takashicompany/endzone34/images/01.jpg

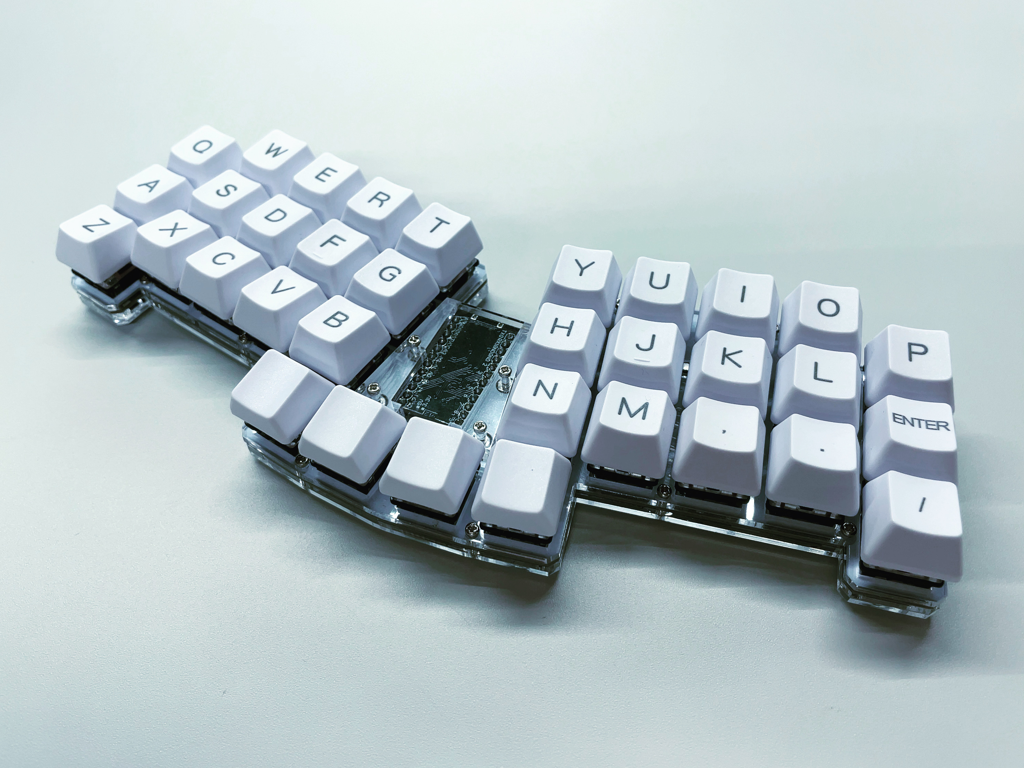
images/01.jpg
