takashicompany/endzone34/images/02.jpg

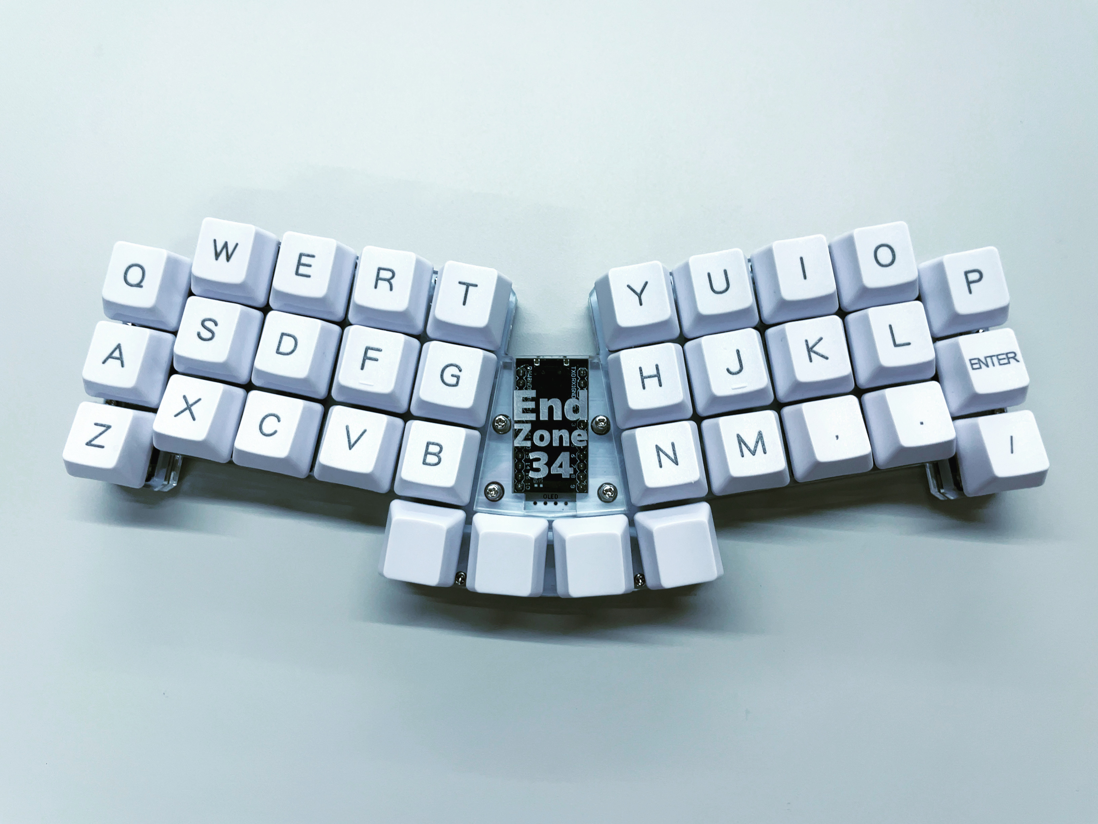
images/02.jpg
