takashicompany/endzone34/images/03.jpg

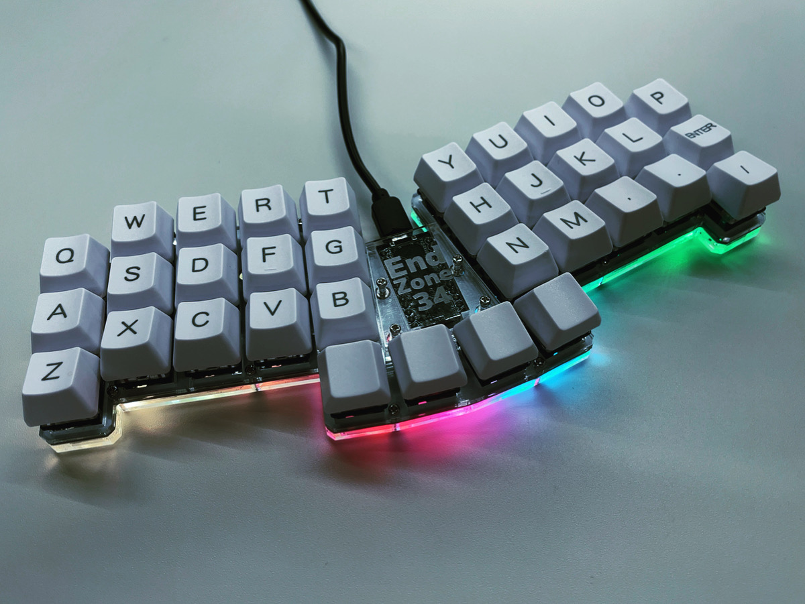
images/03.jpg
