takashicompany/endzone34/images/04.jpg

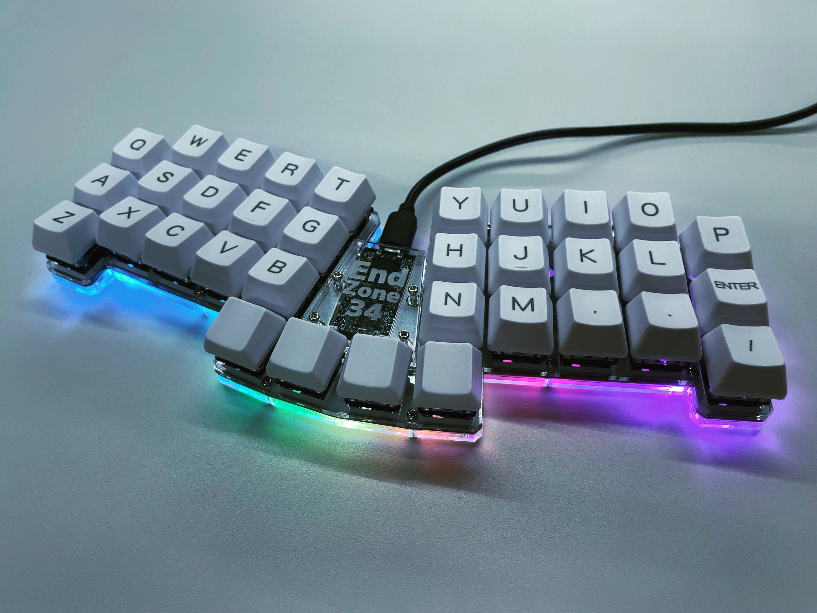
images/04.jpg
