takashicompany/endzone34/images/05.jpg

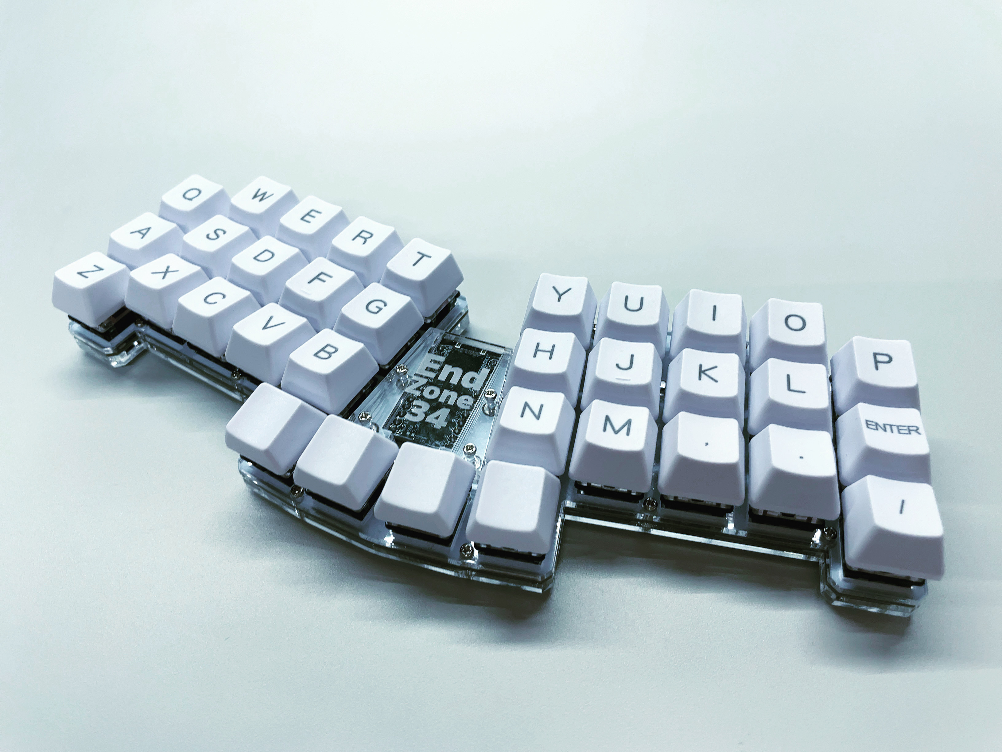
images/05.jpg
