takashicompany/endzone34/images/06.jpg

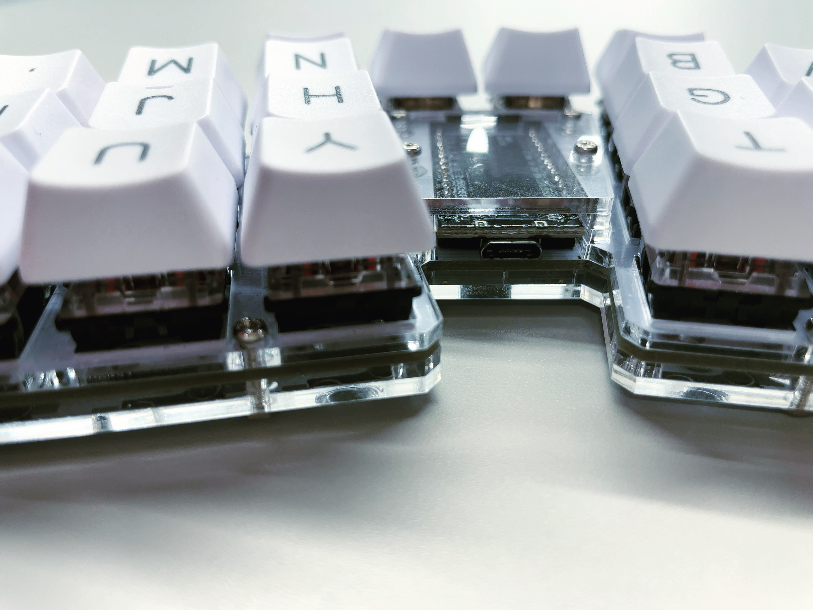
images/06.jpg
