takashicompany/endzone34/images/07.jpg

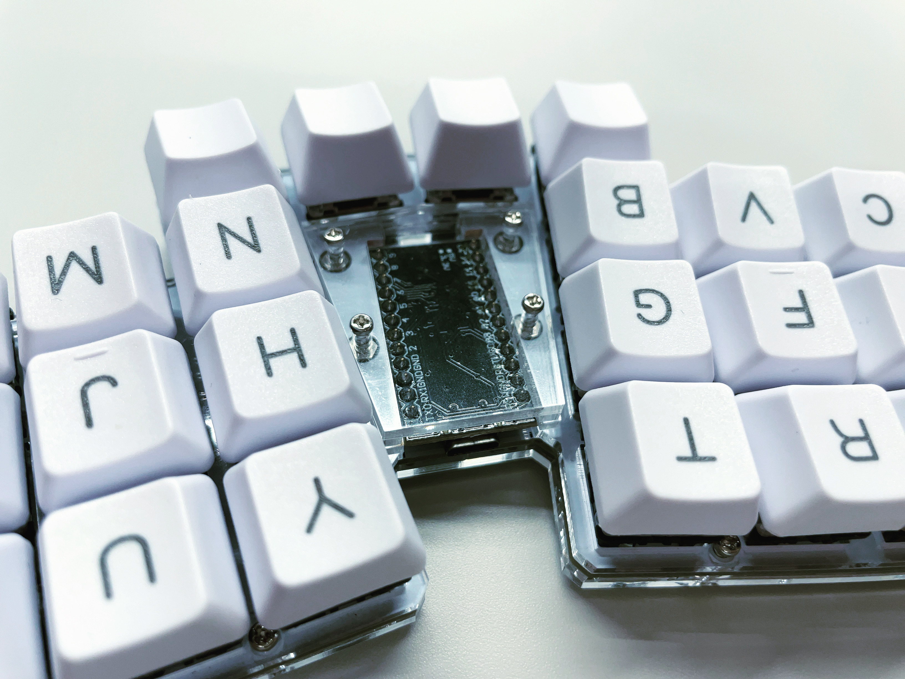
images/07.jpg
