takashicompany/endzone34/images/09.jpg

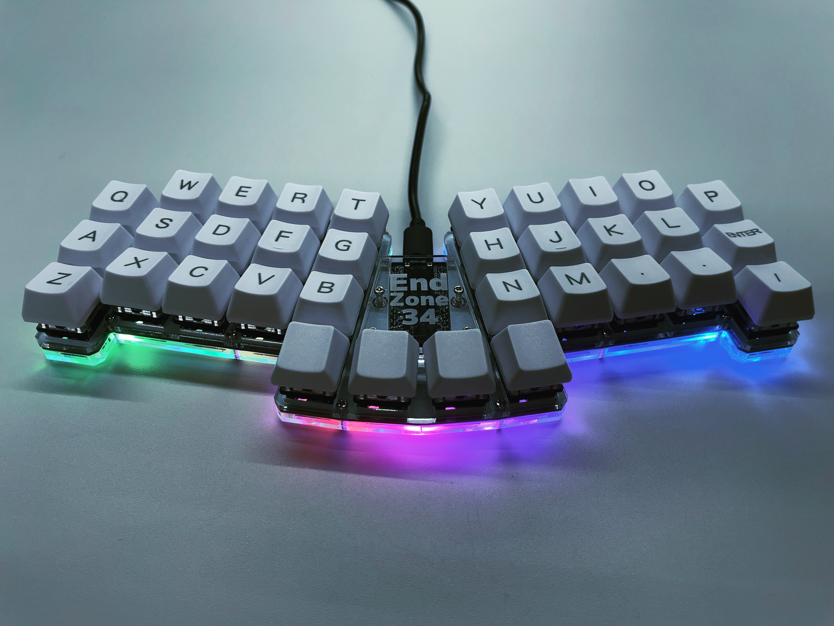
images/09.jpg
