takashicompany/endzone34/images/10.jpg

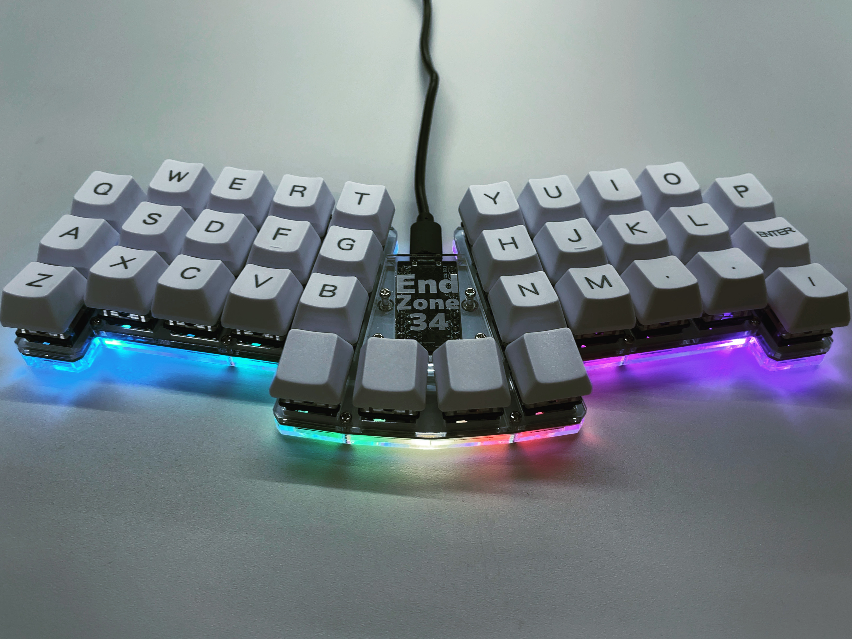
images/10.jpg
