takashicompany/endzone34/images/11.jpg

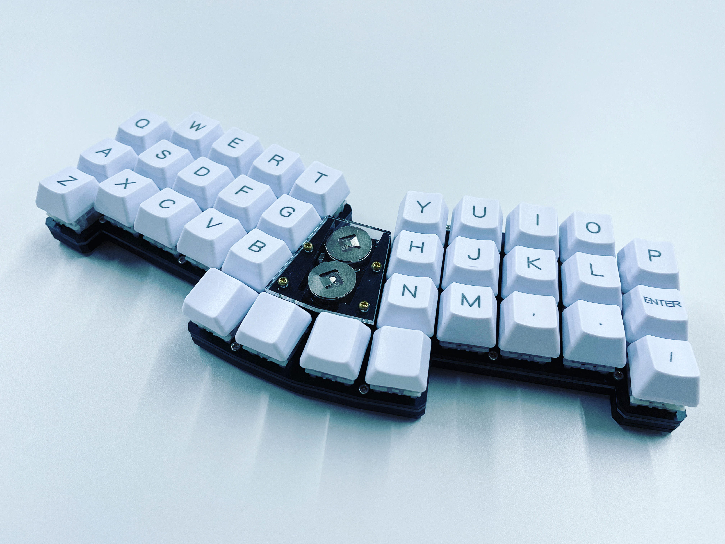
images/11.jpg
