takashicompany/endzone34/images/12.jpg

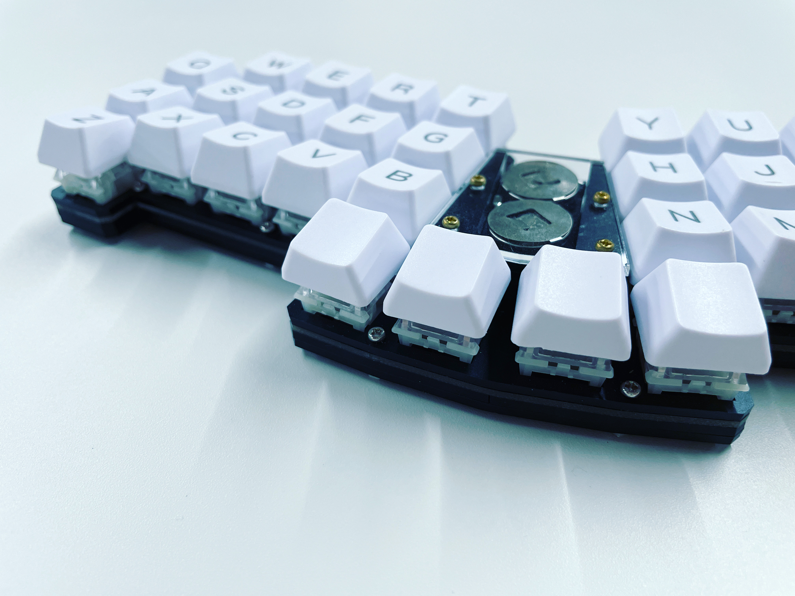
images/12.jpg
