takashicompany/endzone34/images/15.jpg

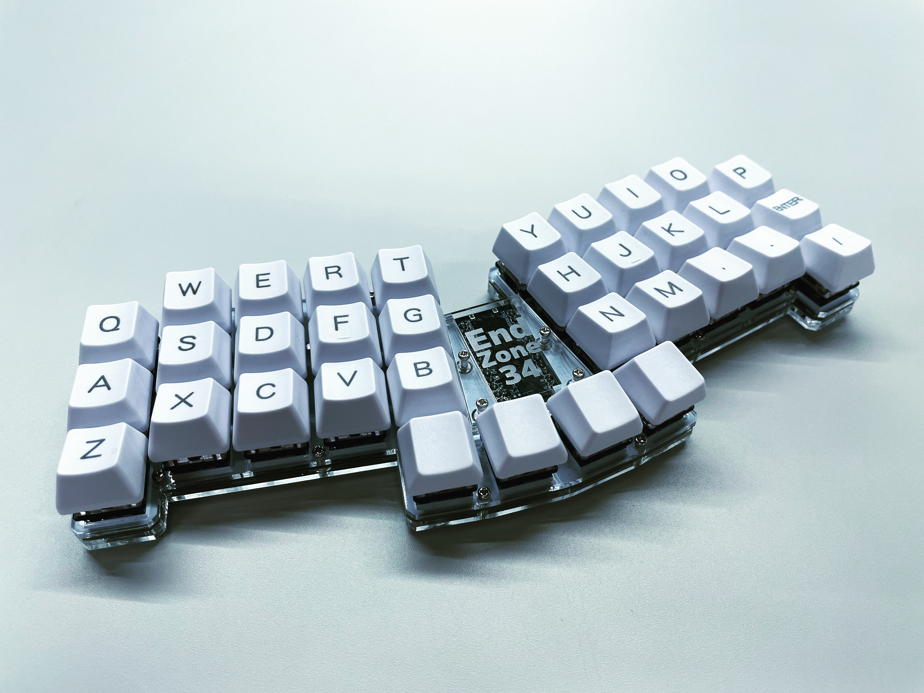
images/15.jpg
