takashicompany/endzone34/images/16.jpg

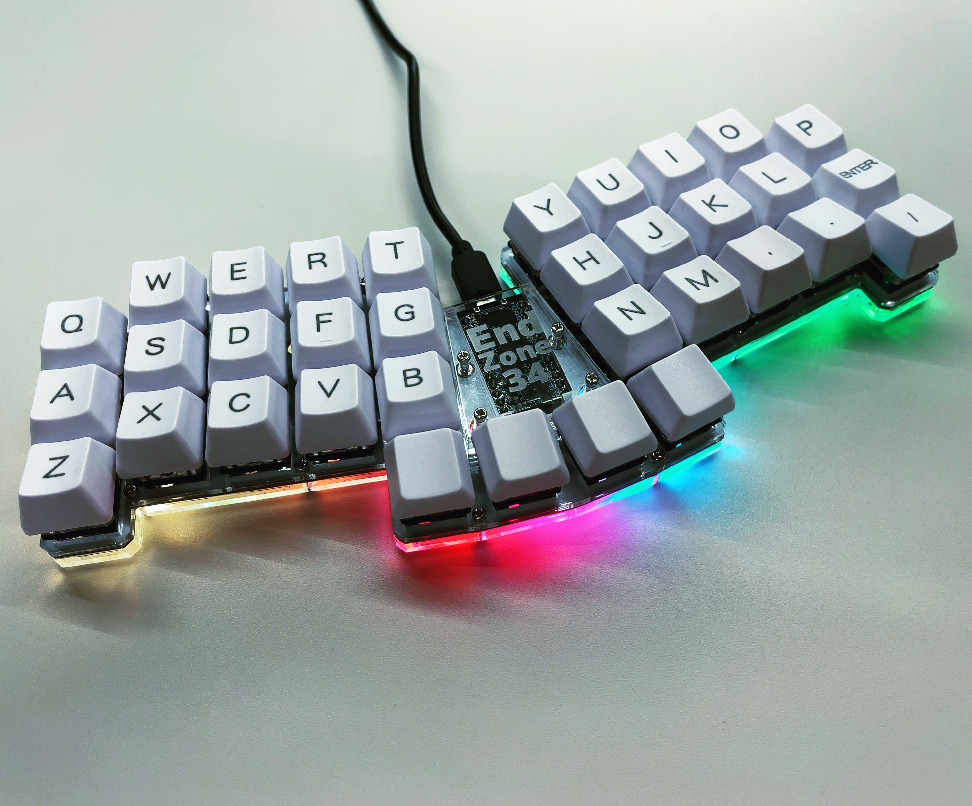
images/16.jpg
