takashicompany/endzone34/images/17.jpg

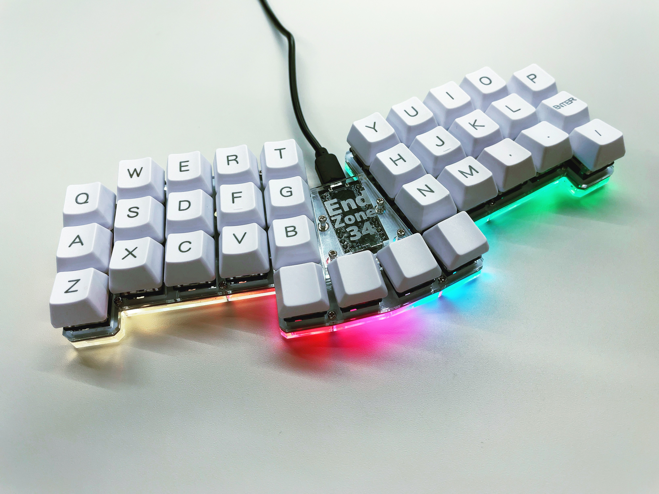
images/17.jpg
