takashicompany/endzone34/images/18.jpg

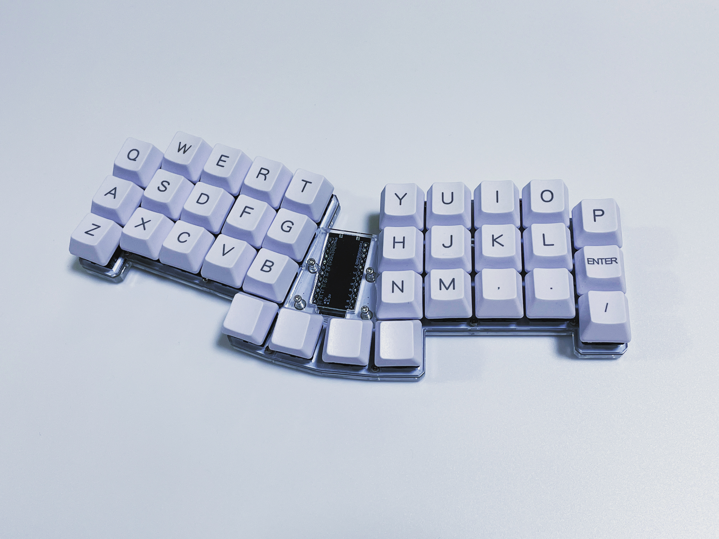
images/18.jpg
