takashicompany/endzone34/images/19.jpg

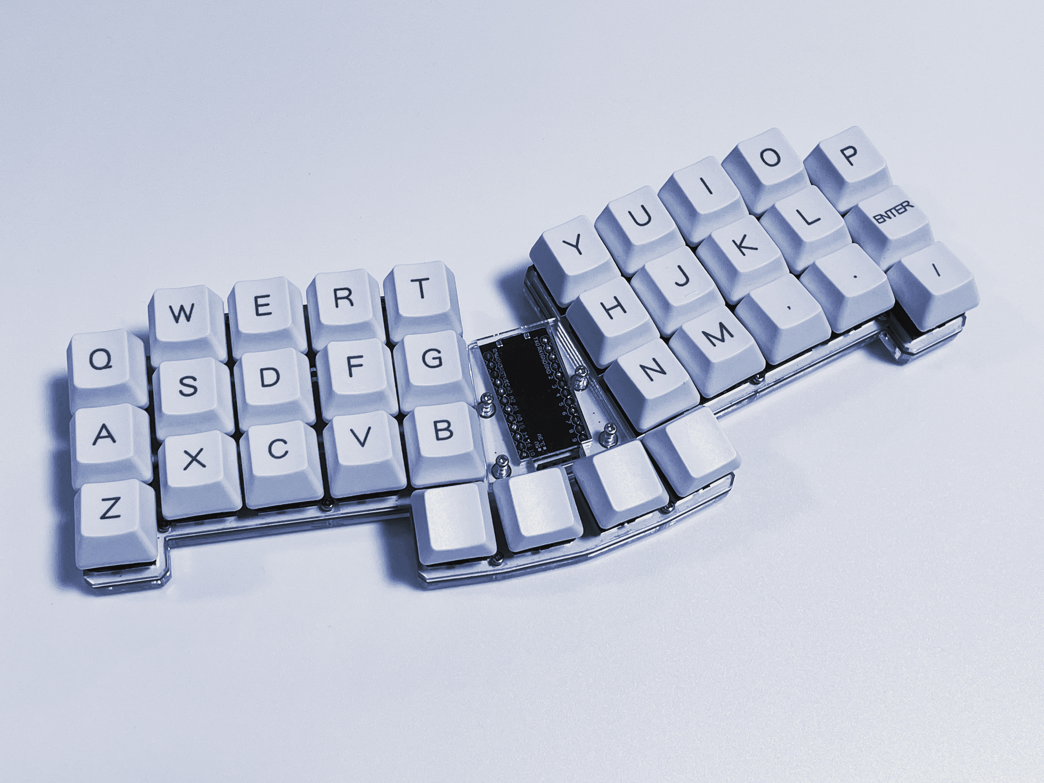
images/19.jpg
