takashicompany/endzone34/images/20.jpg

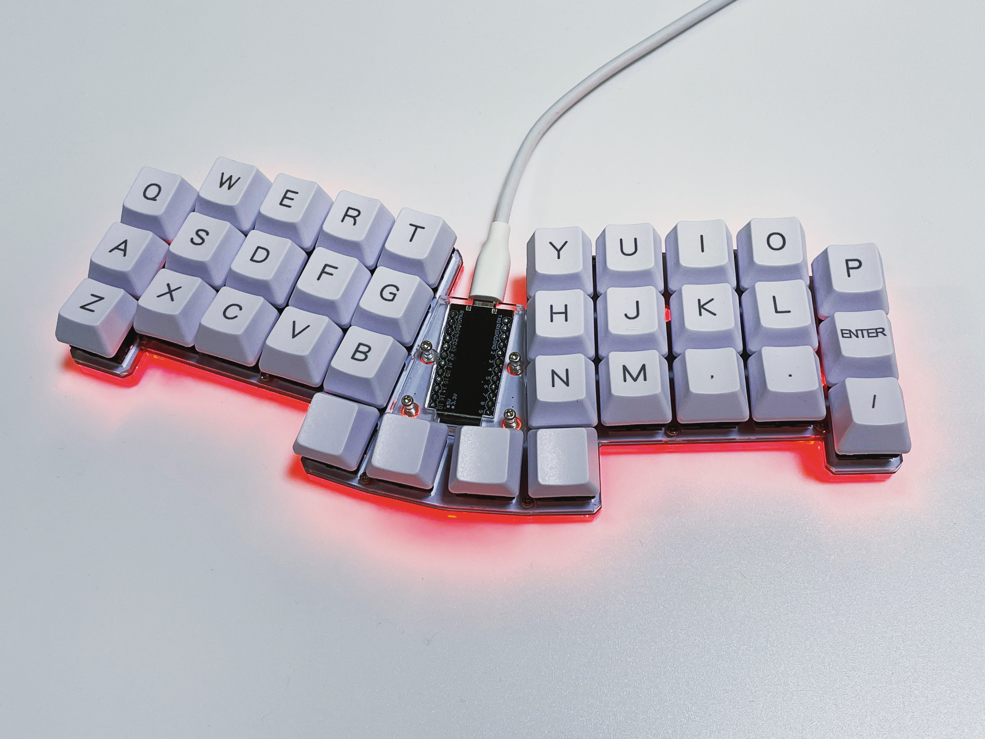
images/20.jpg
