takashicompany/endzone34/images/21.jpg

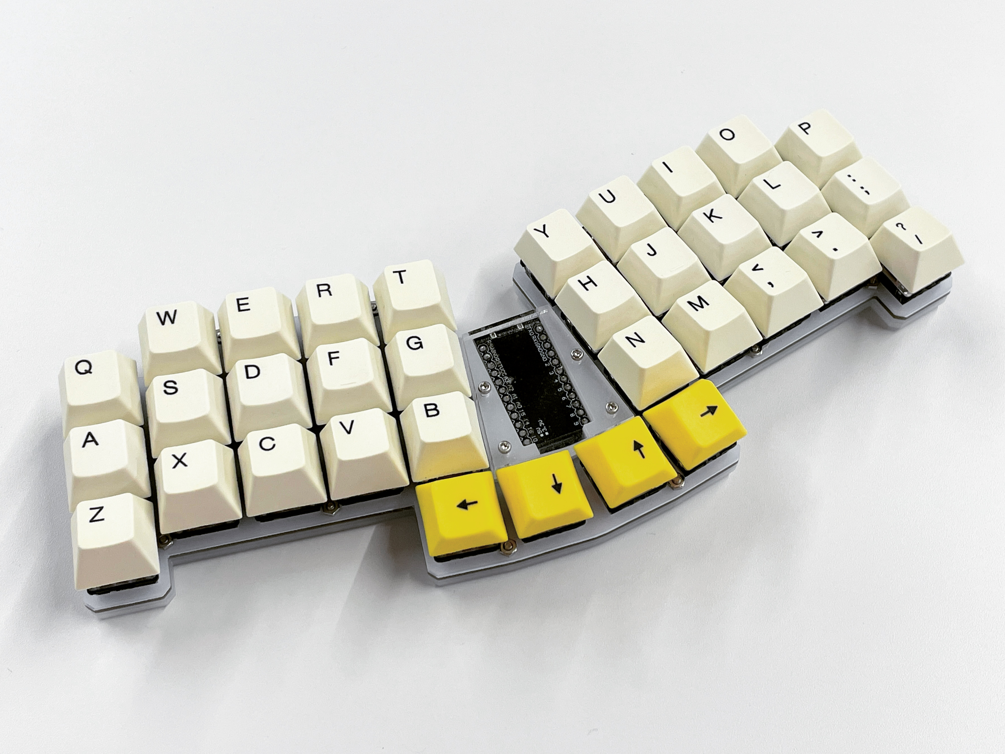
images/21.jpg
