takashicompany/endzone34/images/22.jpg

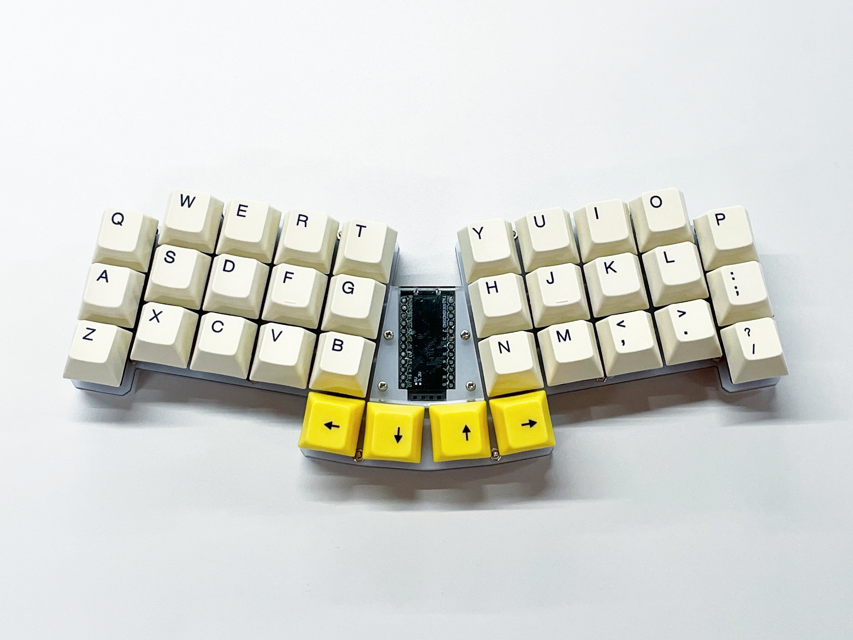
images/22.jpg
