takashicompany/endzone34/images/23.jpg

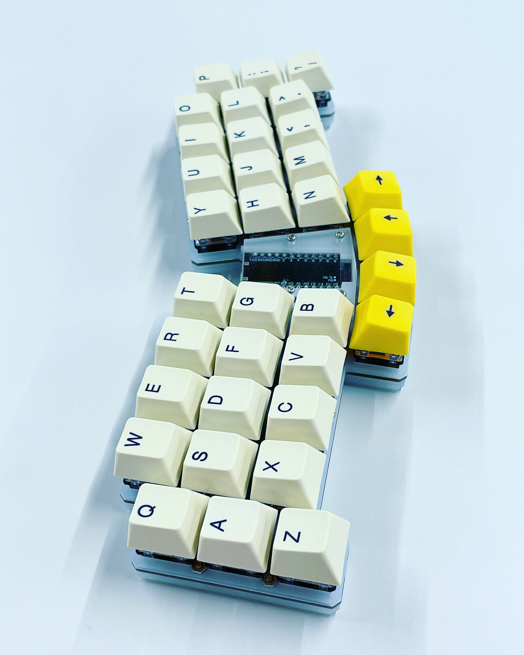
images/23.jpg
