takashicompany/endzone34/images/24.jpg

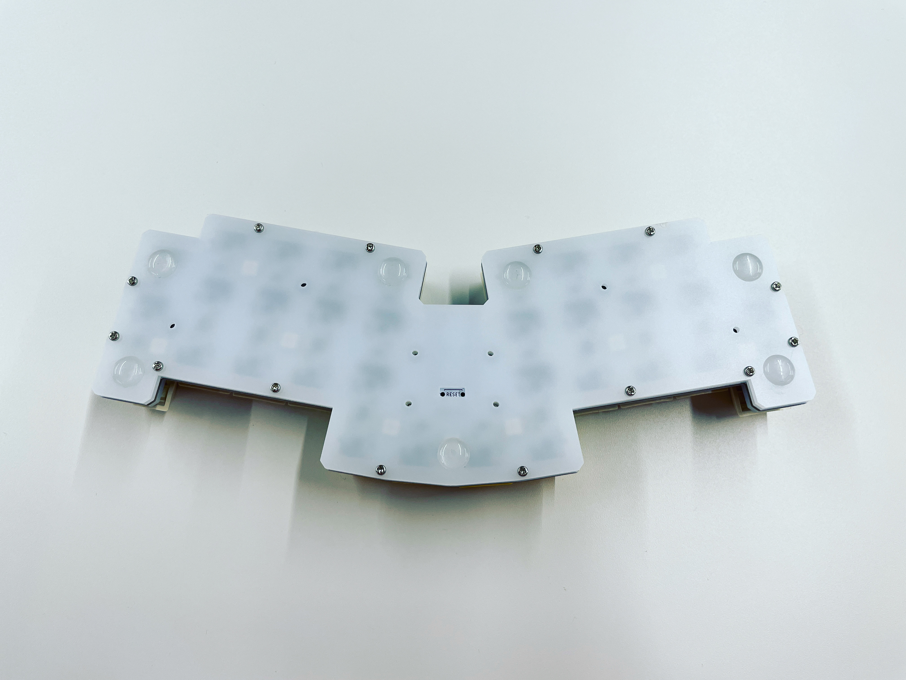
images/24.jpg
