takashicompany/endzone34/images/25.jpg

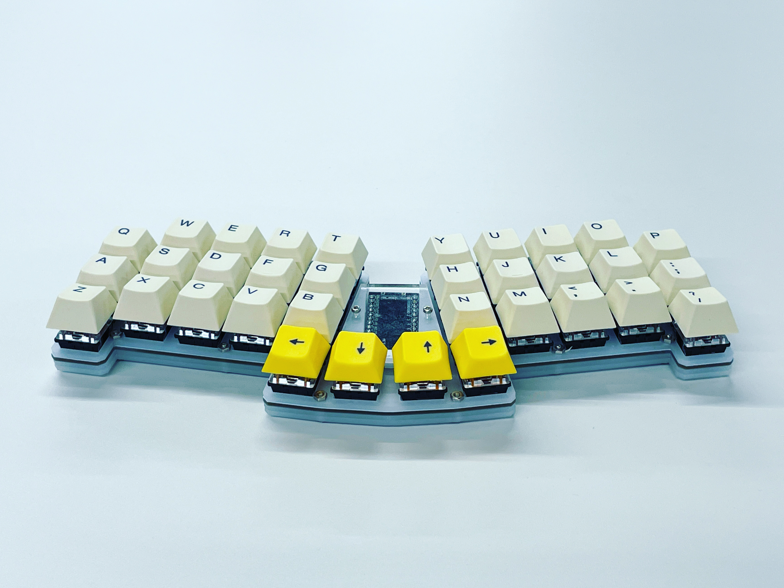
images/25.jpg
