takashicompany/endzone34/images/26.jpg

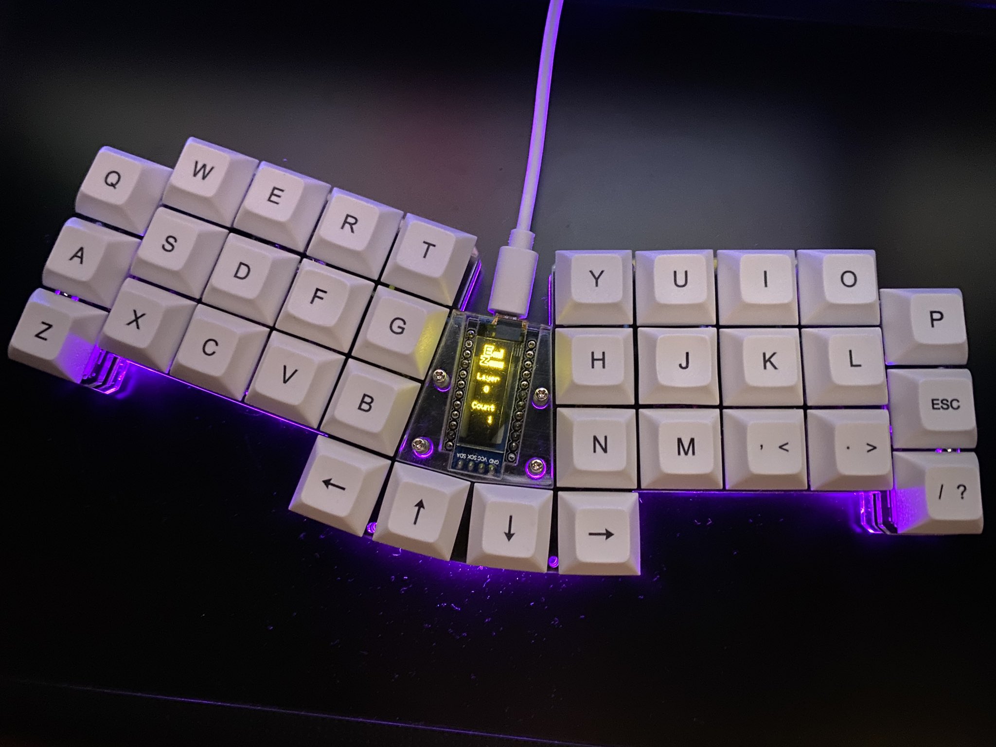
images/26.jpg
