takashicompany/endzone34/images/27.jpg

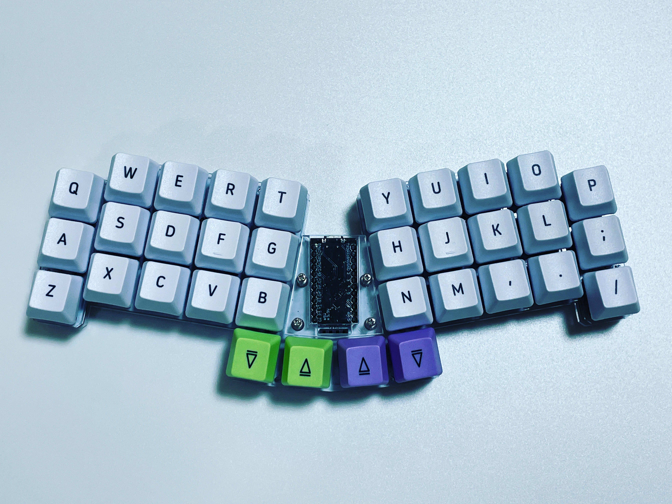
images/27.jpg
