takashicompany/endzone34/images/28.jpg

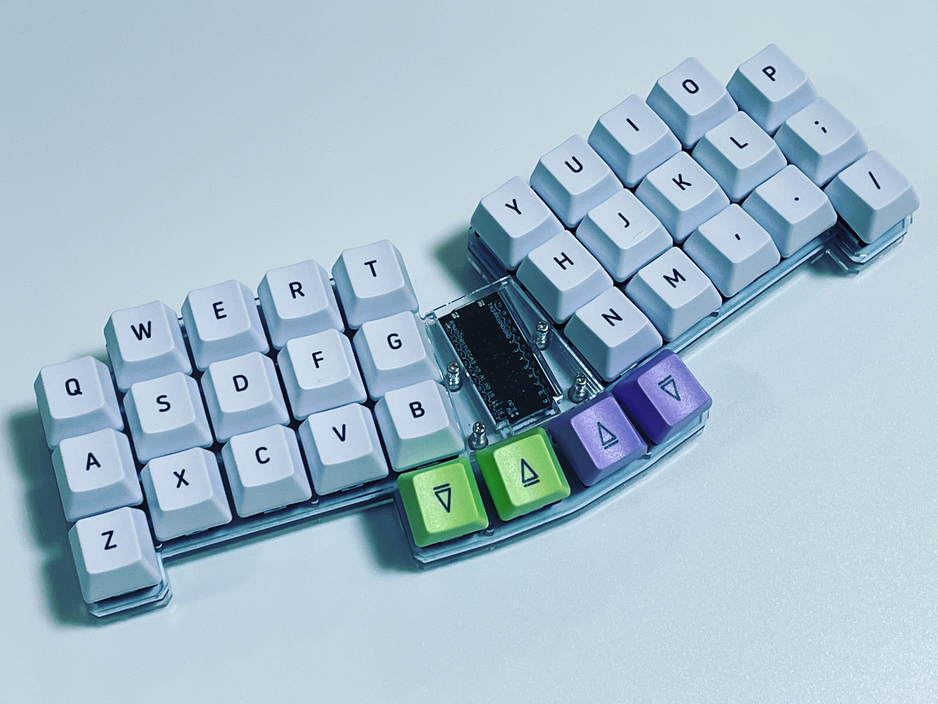
images/28.jpg
