takashicompany/endzone34/images/29.jpg

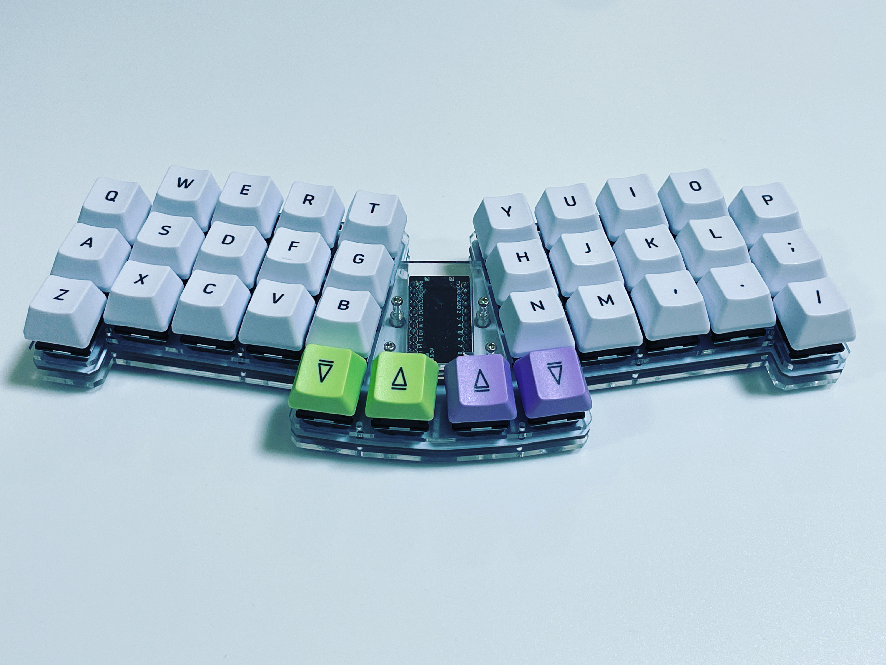
images/29.jpg
