takashicompany/endzone34/images/30.jpg

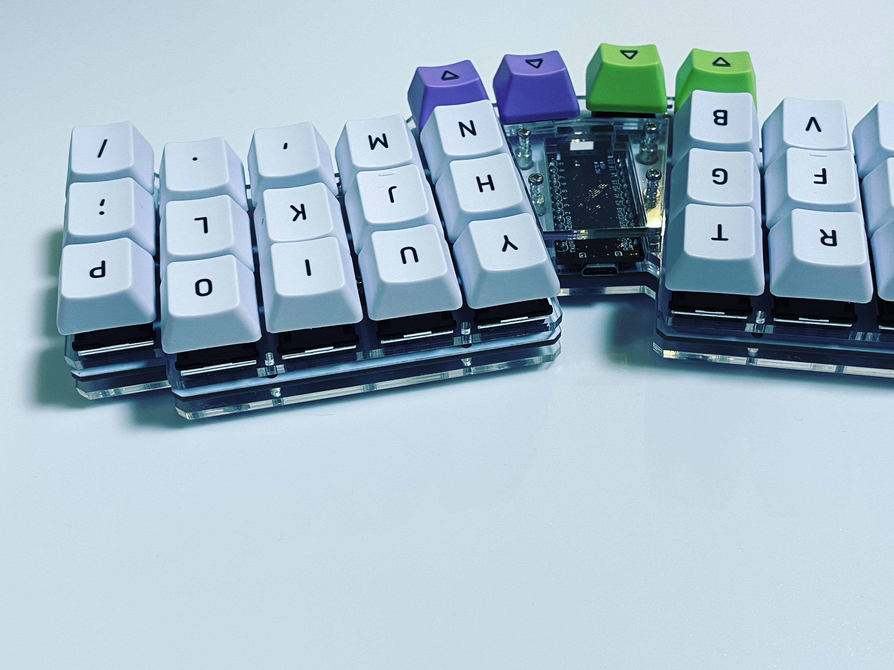
images/30.jpg
