takashicompany/endzone34/images/31.jpg

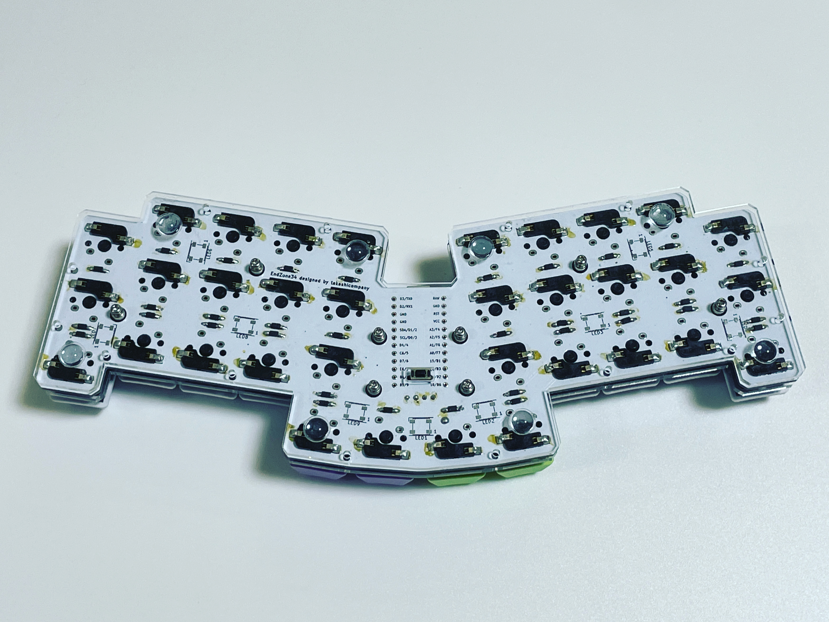
images/31.jpg
