takashicompany/endzone34/images/main.jpg

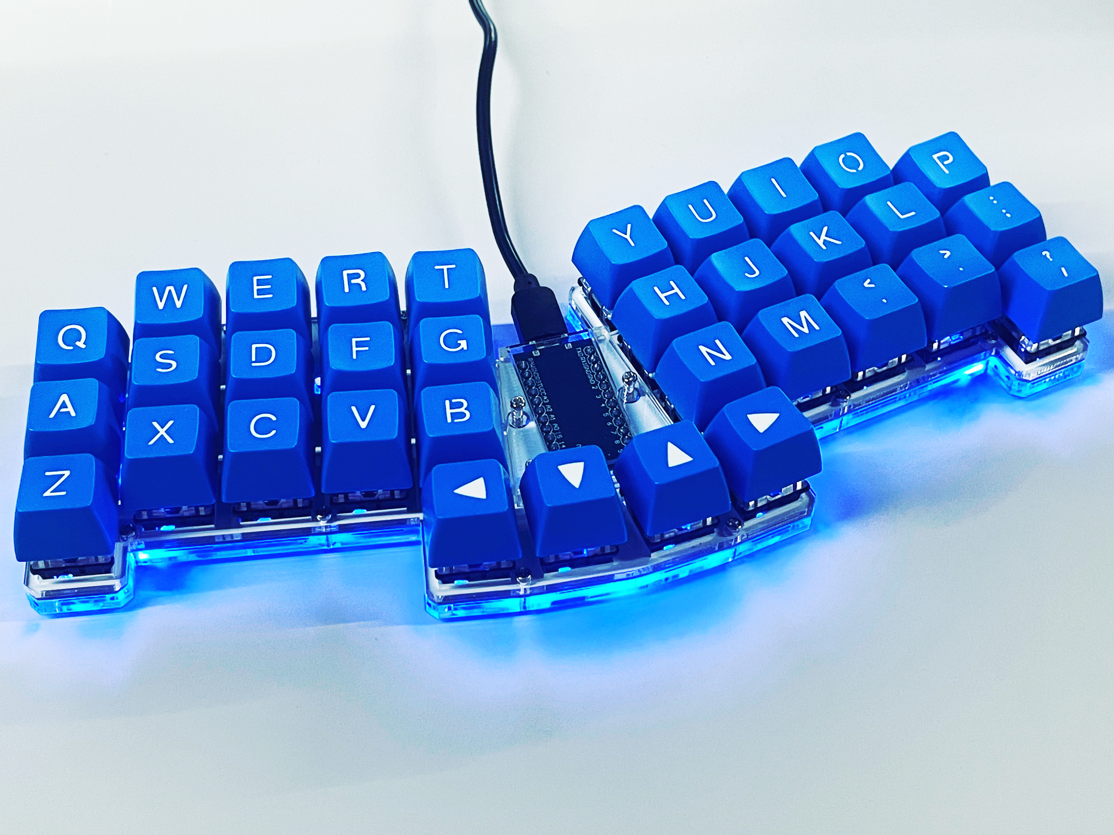
images/main.jpg
